jueta/DIY_DJ_Controller/reference circuits/Screenshot 2026-01-16 at 19.16.51.png

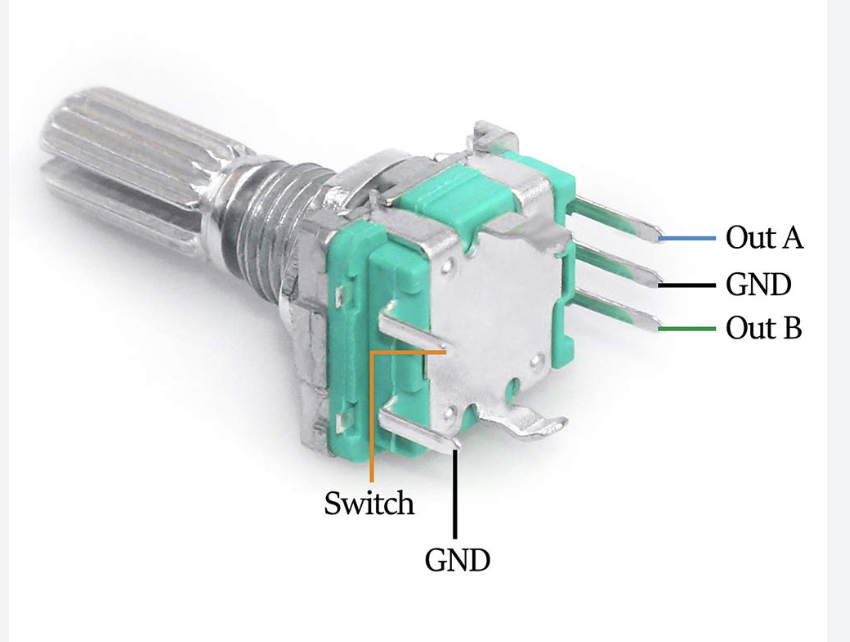
reference circuits/Screenshot 2026-01-16 at 19.16.51.png
