jueta/DIY_DJ_Controller/reference circuits/Screenshot 2026-01-16 at 19.17.04.png

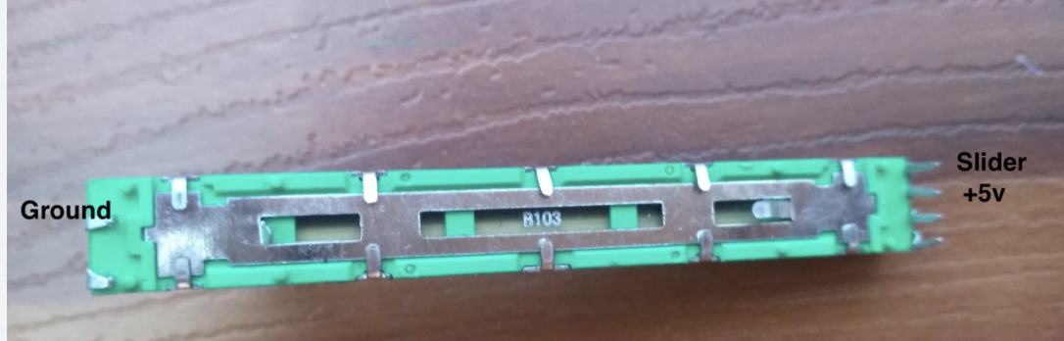
reference circuits/Screenshot 2026-01-16 at 19.17.04.png
